Morfogon/TCC-BabaEletronica/datasets/Dataset_Microfone/Espectrograma Audio Original.png

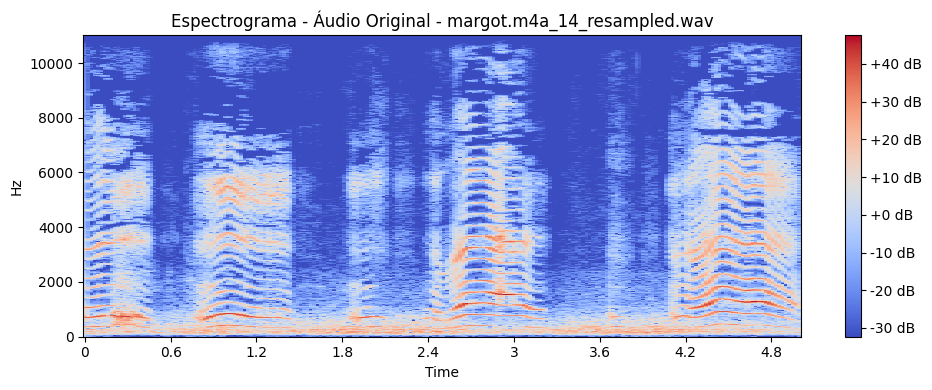
datasets/Dataset_Microfone/Espectrograma Audio Original.png
