Morfogon/TCC-BabaEletronica/datasets/Dataset_Microfone/Espectrograma Audio passado pelo Microfone.png

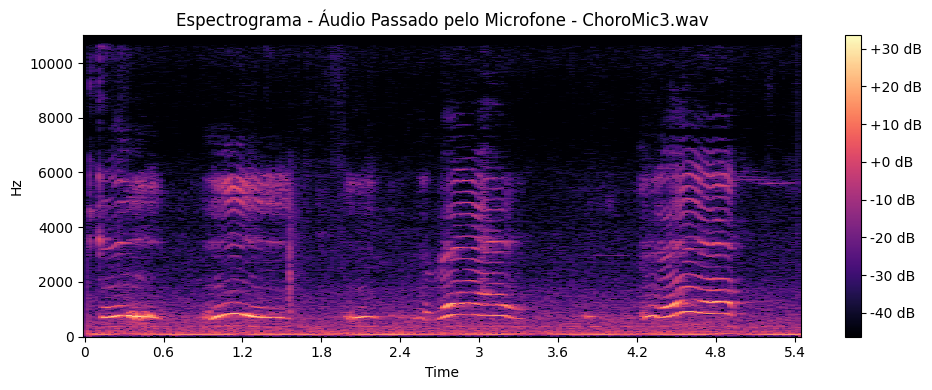
datasets/Dataset_Microfone/Espectrograma Audio passado pelo Microfone.png
