Morfogon/TCC-BabaEletronica/Modelos_3D/Novo-Fundo-Caixa-baba.SLDPRT

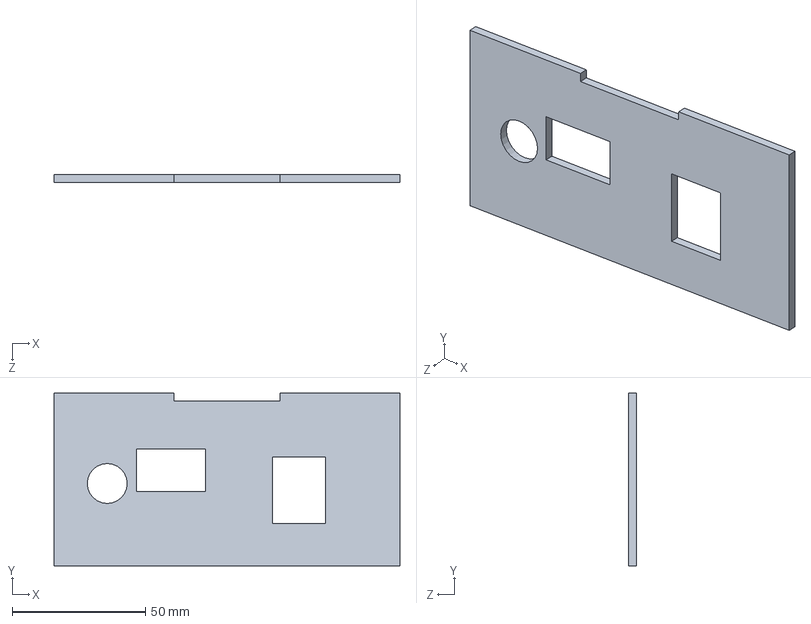
[picture p23: CAD file, 2024-02-28]
Modelos_3D/Novo-Fundo-Caixa-baba.SLDPRT
130.0 x 65.0 x 3.00 mm
