Morfogon/TCC-BabaEletronica/Modelos_3D/Caixa-baba-Tampa.SLDPRT

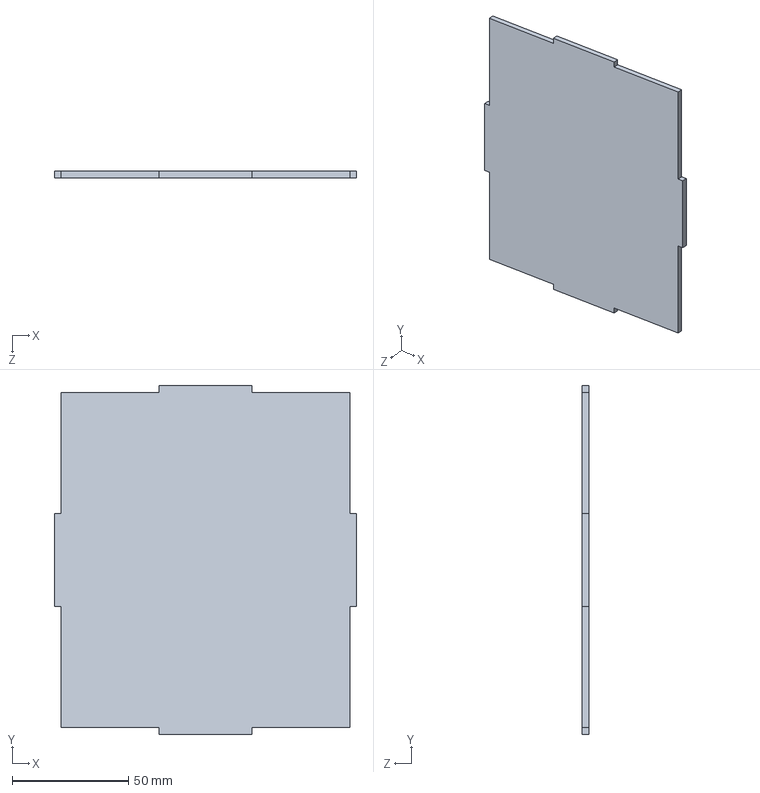
[picture p24: CAD file, 2024-02-28]
Modelos_3D/Caixa-baba-Tampa.SLDPRT
130.0 x 150.0 x 3.00 mm
