Morfogon/TCC-BabaEletronica/Modelos_3D/Bracelete_Pai.SLDPRT

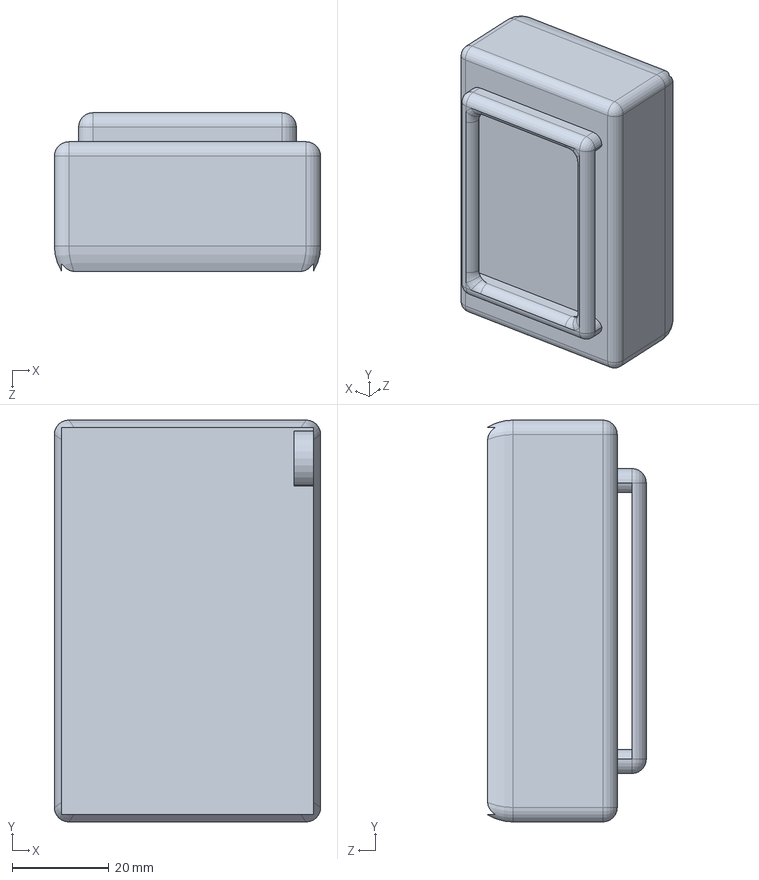
[picture p28: CAD file, 2024-02-28]
Modelos_3D/Bracelete_Pai.SLDPRT
55.0 x 83.0 x 32.8 mm
