Morfogon/TCC-BabaEletronica/Modelos_3D/JoaoVitor_TampaBraceleteBebe_3D_1.STL

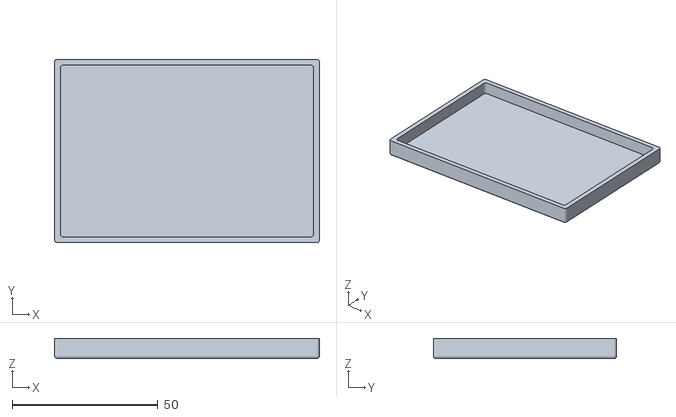
[picture p29: CAD file, 2024-02-28]
Modelos_3D/JoaoVitor_TampaBraceleteBebe_3D_1.STL
91.0 x 63.0 x 7.00
