Morfogon/TCC-BabaEletronica/Modelos_3D/JoaoVitor_Caixa-Luz-Lateral1Nova_laser_1.DXF

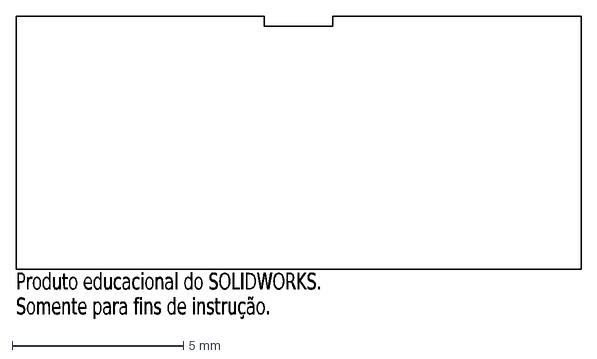
[picture p31: CAD file, 2024-02-28]
Modelos_3D/JoaoVitor_Caixa-Luz-Lateral1Nova_laser_1.DXF
Produto educacional do SOLIDWORKS.
Somente para fins de instrução.
