Morfogon/TCC-BabaEletronica/Modelos_3D/Base-Nova-caixa-luz.SLDPRT

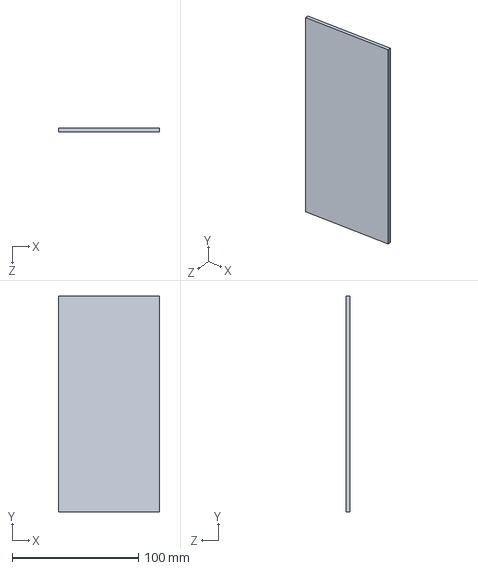
[picture p32: CAD file, 2024-02-28]
Modelos_3D/Base-Nova-caixa-luz.SLDPRT
80.0 x 171.0 x 3.00 mm
