Morfogon/TCC-BabaEletronica/Modelos_3D/Lateral-baba-nova.SLDPRT

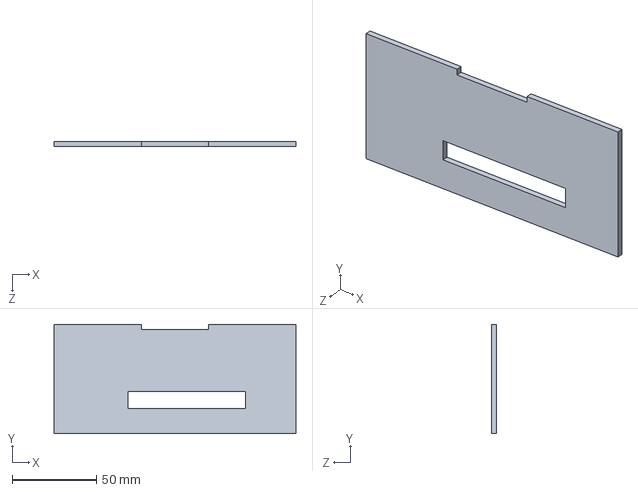
[picture p33: CAD file, 2024-02-28]
Modelos_3D/Lateral-baba-nova.SLDPRT
144.0 x 65.0 x 3.00 mm
