Morfogon/TCC-BabaEletronica/Modelos_3D/Bracelete_Bebe.SLDPRT

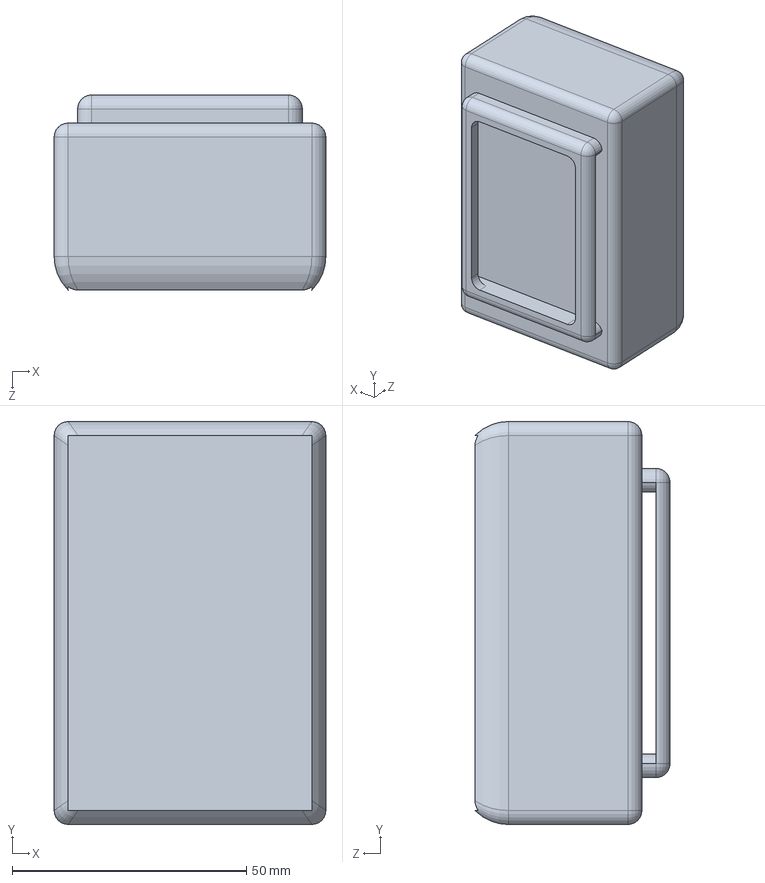
[picture p35: CAD file, 2024-02-28]
Modelos_3D/Bracelete_Bebe.SLDPRT
58.0 x 86.0 x 41.6 mm
