Morfogon/TCC-BabaEletronica/Modelos_3D/Caixa-baba.SLDPRT

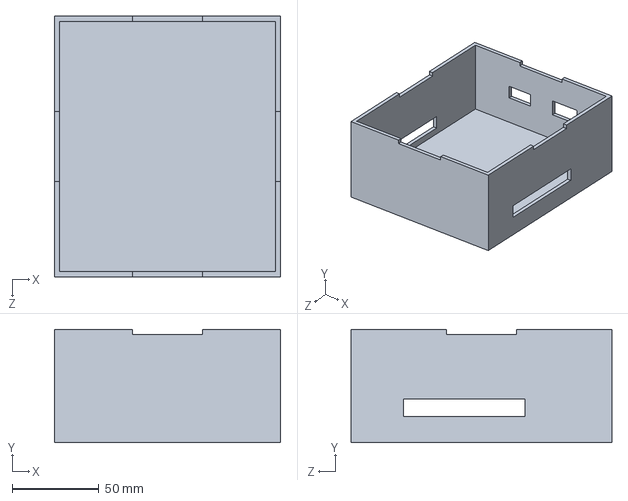
[picture p38: CAD file, 2024-02-28]
Modelos_3D/Caixa-baba.SLDPRT
130.0 x 65.0 x 150.0 mm
