Morfogon/TCC-BabaEletronica/Modelos_3D/Fundo-Novo-caixa-luz.SLDPRT

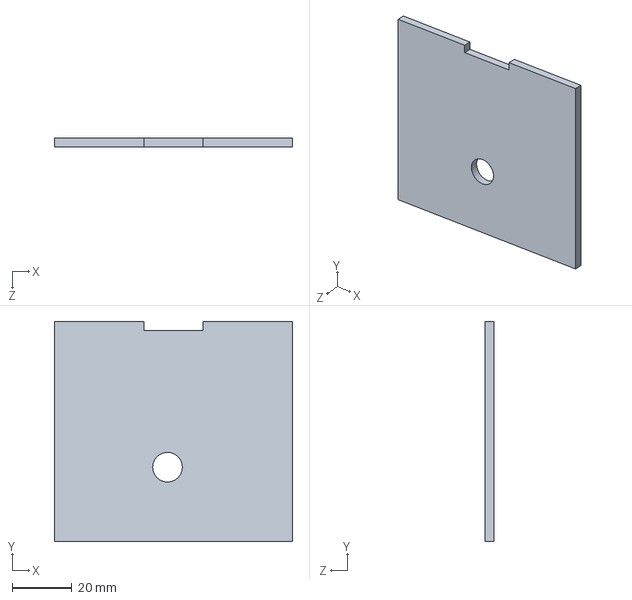
[picture p43: CAD file, 2024-02-28]
Modelos_3D/Fundo-Novo-caixa-luz.SLDPRT
80.0 x 74.0 x 3.00 mm
